fgsect/EM-Fault-It-Yourself/emfi_station/attack.py

# EMFI Station - Orchestrate electromagnetic fault injection attacks
# Copyright (C) 2022 Niclas Kühnapfel
#
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
import logging


class Attack:
    """
    Base class for the attack implementations.
    """
    def __init__(self, start_pos: tuple[float, float, float], end_pos: tuple[float, float, float], step_size: int,
                 max_target_temp: float = 40, cooling: float = 0):
        """
        Initializes attack settings and attack hardware.
        :param start_pos: Start position of attack.
        :param end_pos: End positions of attack.
        :param step_size: End positions of attack.
        :param max_target_temp: Maximum target temperature before attack is paused.
        :param cooling: Target cooling fan speed (0-1)
        """
        self.log = logging.getLogger(__name__)
        self.start_pos = start_pos or [0, 0, 0]
        self.end_pos = end_pos or [0, 0, 0]
        self.step_size = step_size or 1
        self.max_target_temp = max_target_temp
        self.cooling = cooling

    @staticmethod
    def name() -> str:
        """
        Returns name of target/attack.
        :return: Attack name
        """
        return 'Default'

    def init(self) -> None:
        """
        Initialize hardware and define e.g. ChipShouter settings.
        :return: None
        """
        return None

    def shout(self) -> None:
        """
        Shout procedure.
        :return: None
        """
        return None

    def was_successful(self) -> bool:
        """
        Determines if attack was successful or not.
        Returns True if successful.
        :return: True or False
        """
        return False

    def reset_target(self) -> None:
        """
        Resets the target after an attack.
        :return: None
        """
        return None

    def critical_check(self) -> bool:
        """
        Runs critical checks after every shout. May wait some time.
        Returns False if check failed which leads to a shutdown.
        :return: True or False
        """
        return True
